SuperTuxii/PortableControlPanel/CAD/step_files/Panel-MagnetConnector.step

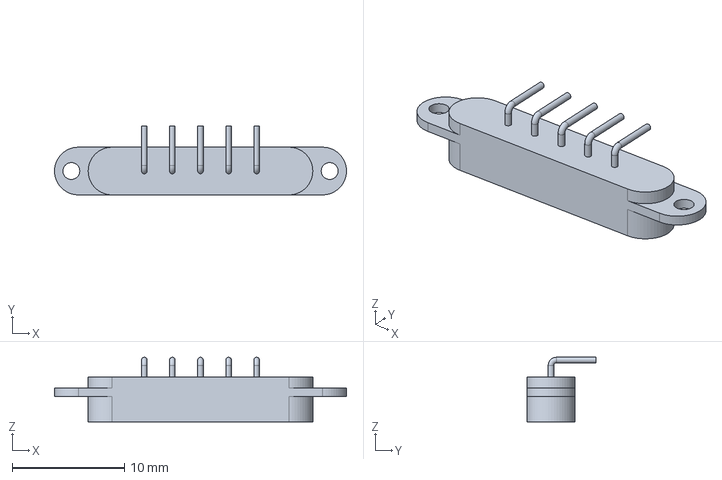
[picture p23: CAD file, 2026-04-25]
CAD/step_files/Panel-MagnetConnector.step
26.0 x 6.12 x 5.75 mm
