SuperTuxii/PortableControlPanel/CAD/step_files/Panel-Speaker.step

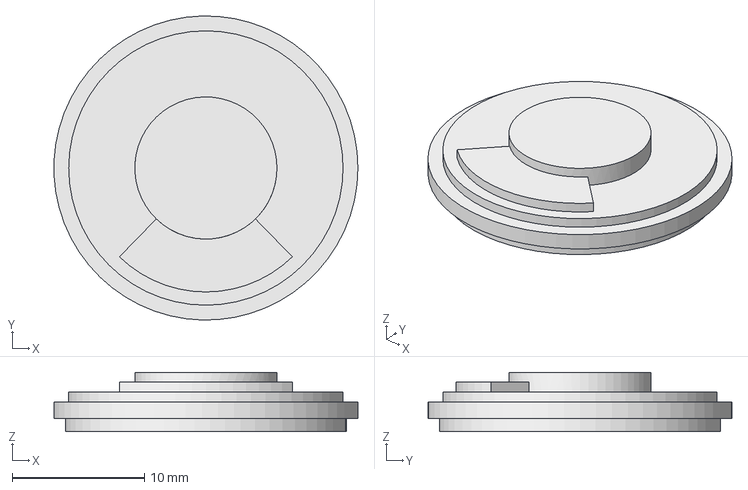
[picture p24: CAD file, 2026-04-25]
CAD/step_files/Panel-Speaker.step
23.0 x 23.0 x 4.50 mm
