SuperTuxii/PortableControlPanel/CAD/step_files/Panel-UsbConnector.step

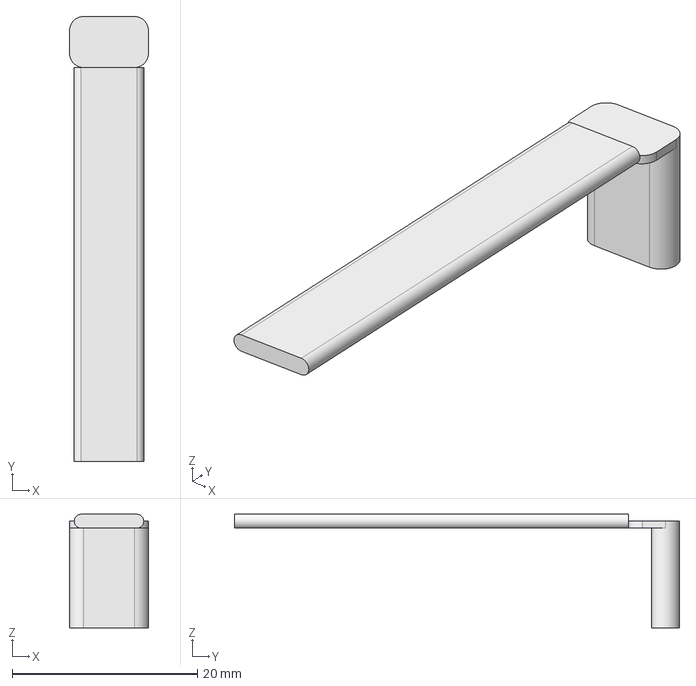
[picture p25: CAD file, 2026-04-25]
CAD/step_files/Panel-UsbConnector.step
8.50 x 48.0 x 12.2 mm
