SuperTuxii/PortableControlPanel/firmware/main/util.h

#ifndef CONTROLPANELFIRMWARE_UTIL_H
#define CONTROLPANELFIRMWARE_UTIL_H
#include <inttypes.h>

int32_t convertDataToInt32(const uint8_t *data);
uint16_t convertDataToUInt16(const uint8_t *data);

#endif //CONTROLPANELFIRMWARE_UTIL_H
